ktanino10/copilot-brick-display/docs/licensing.md

# Notices and rights

No blanket license has been selected for this project's original code, CAD, artwork, or documents.
Public availability is not a statement that all uses are permitted. Ask the repository owner
about reuse terms. This file does not relabel third-party components.

Third-party material intentionally redistributed:

| Material | License / notice location | Purpose |
| --- | --- | --- |
| Three.js 0.180.0 | MIT, `site/vendor/THREE-LICENSE.txt` | Local browser 3D runtime |
| B612 Mono Bold | SIL Open Font License 1.1, `resources/fonts/OFL.txt` | Exact approved message outlines |
| Barlow Condensed Bold / Black | SIL Open Font License 1.1, `resources/fonts/barlow-condensed/OFL.txt` | Main-line openings and enlarged URL lettering |

Python packages, FreeCAD, Blender and ffmpeg are build/runtime tools rather than vendored
application binaries. Their respective licenses remain applicable. Package versions are pinned
where installed for this project. Source-reference PDFs and unmodified private/reference photographs
are not copied into the public package.

The [build log](build-log.ja.md) includes only privacy-redacted derivatives of user-supplied progress
photographs, authorized for this project's public and private repository build records.
The photographs remain the rights holder's material: no model/library license automatically
applies to them, and this permission is not CC0, third-party redistribution permission or approval
to repost to MakerWorld or other services. Original photos and identifying metadata are not distributed.

The unmodified Bold font was obtained from the official Google Fonts `ofl/barlowcondensed`
directory at commit `e44c4b011a820c2cbe2fd2cfa8052037d7edb571`.
Its SHA256 is `e476562ec9c1e16cf16475895b511f08c804f438cc9a9f80a44ea50a0eeb5b65`.
The OFL notice is retained unchanged. Per-glyph manufactured counter edits do not modify or relicense the font file.

The new front logo is a supported 3D relief derived from the user's supplied GitHub mark.
Only the derived contours and manufactured geometry are included; the input raster is not distributed.
This does not grant a blanket trademark license or claim official status.

LEGO, Bambu Lab and GitHub names identify references, intended interfaces, tools or the public
profile URL. This is an original, unofficial personal display model. It is not an official LEGO
or GitHub product and has no endorsement or compatibility certification from those organizations.
