ktanino10/copilot-brick-display/site/media/A-base-front.png

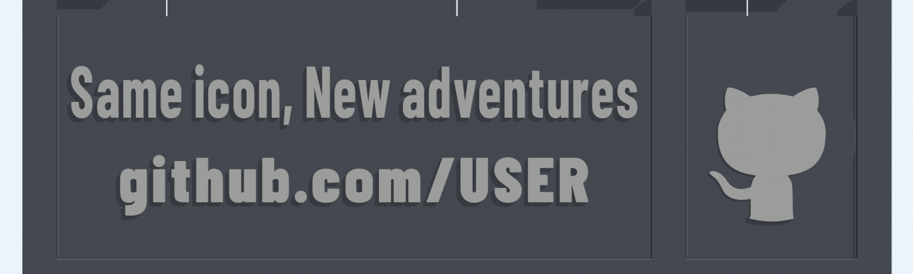
site/media/A-base-front.png
