ktanino10/copilot-brick-display/site/media/A-compare.png

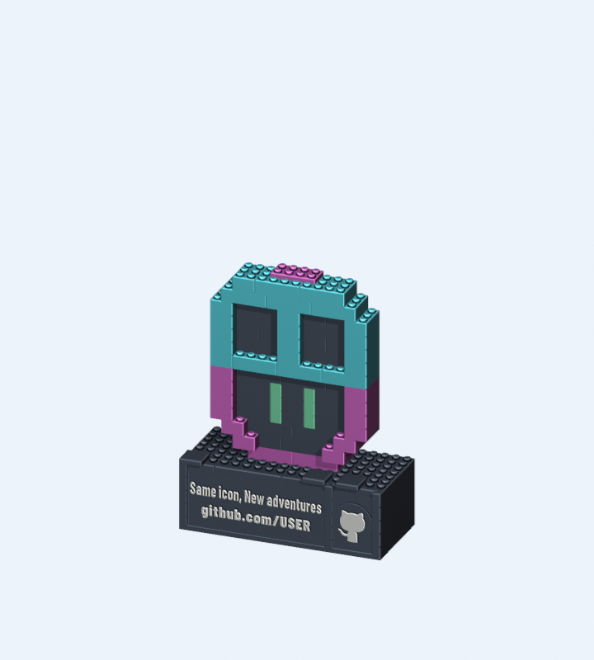
site/media/A-compare.png
