ktanino10/copilot-brick-display/site/media/A-hero.png

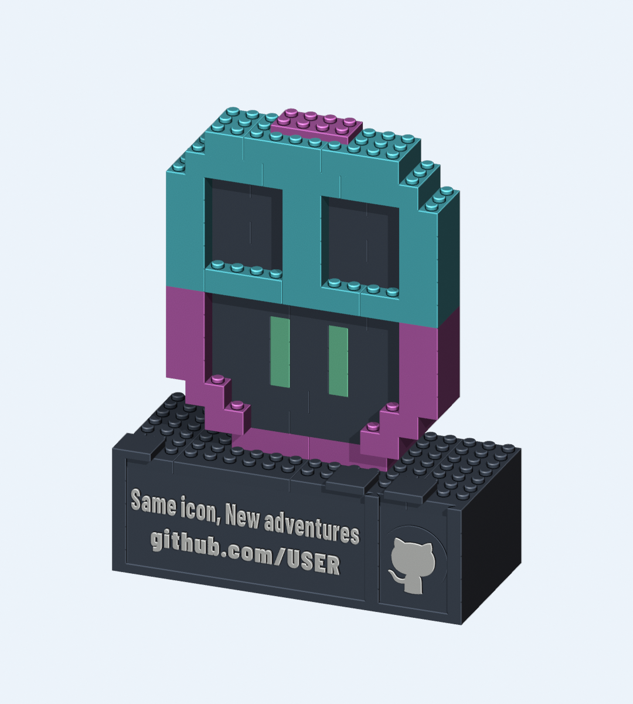
site/media/A-hero.png
