ktanino10/copilot-brick-display/site/media/B-base-front.png

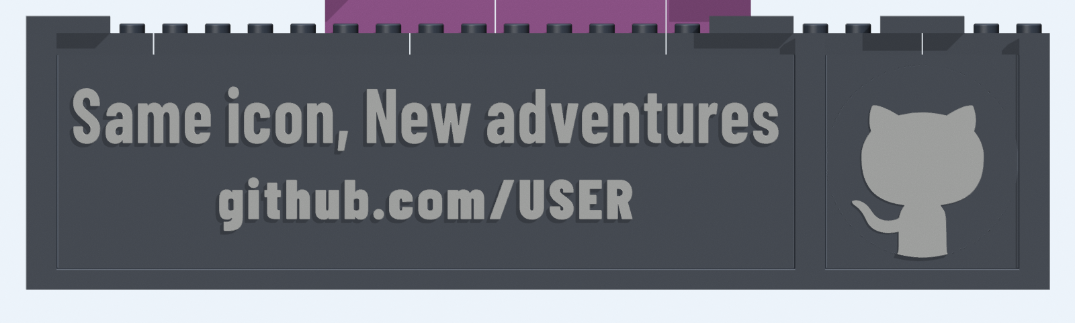
site/media/B-base-front.png
