ktanino10/copilot-brick-display/site/media/B-compare.png

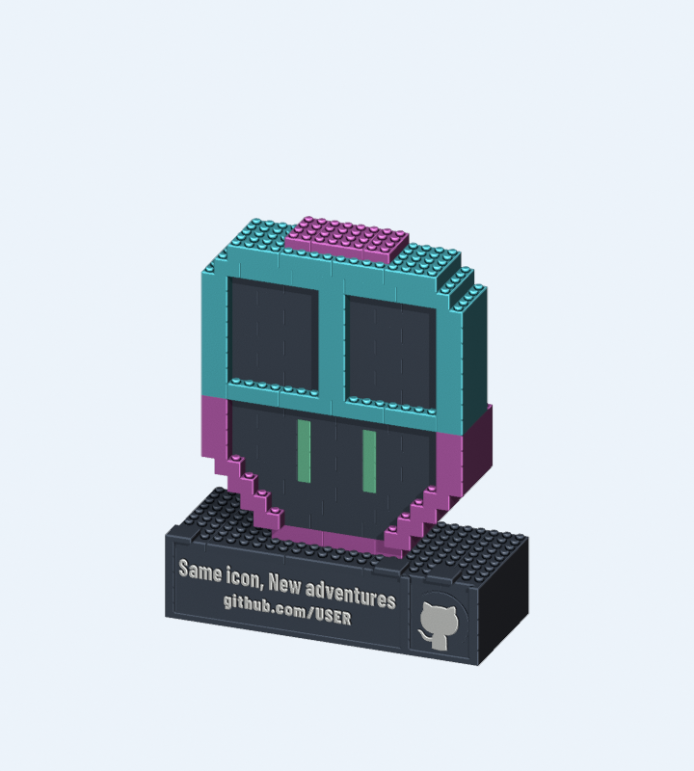
site/media/B-compare.png
