ktanino10/copilot-brick-display/site/media/B-hero.png

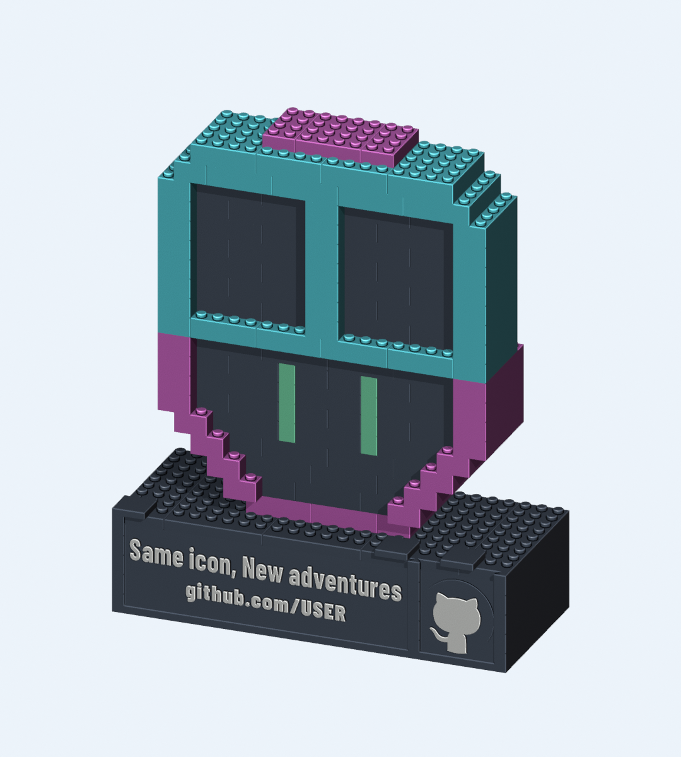
site/media/B-hero.png
