ktanino10/copilot-brick-display/site/media/C-base-front.png

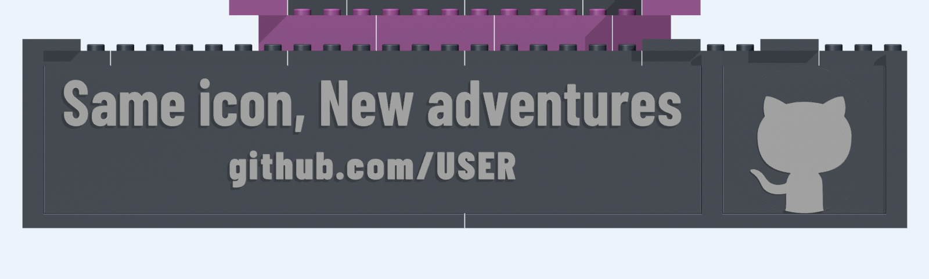
site/media/C-base-front.png
