ktanino10/copilot-brick-display/site/media/C-compare.png

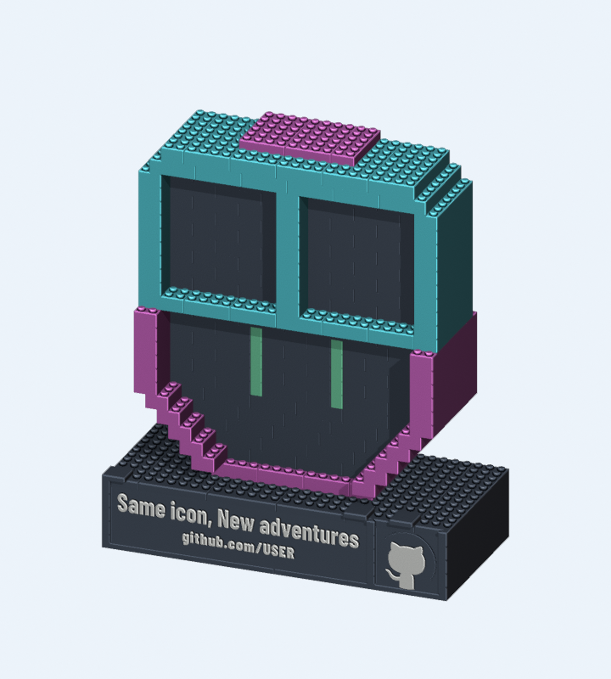
site/media/C-compare.png
