ktanino10/copilot-brick-display/site/media/lettering/A-lettering-before-after.png

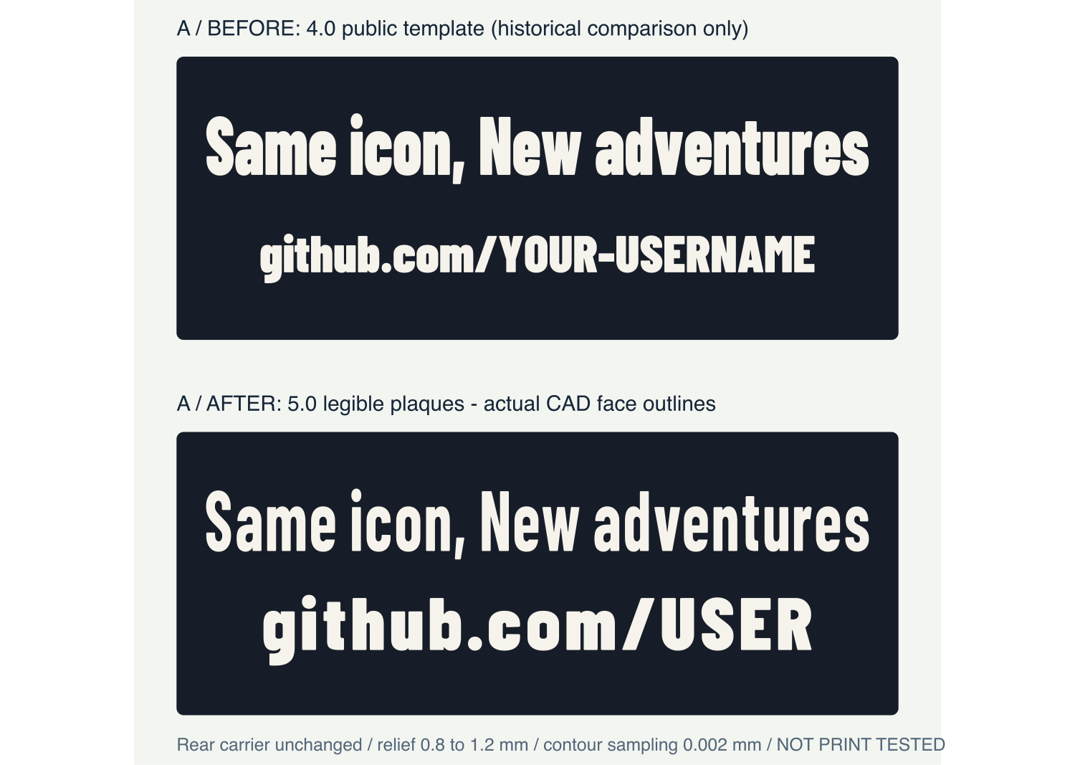
site/media/lettering/A-lettering-before-after.png
