ktanino10/copilot-brick-display/site/media/lettering/C-lettering-before-after.png

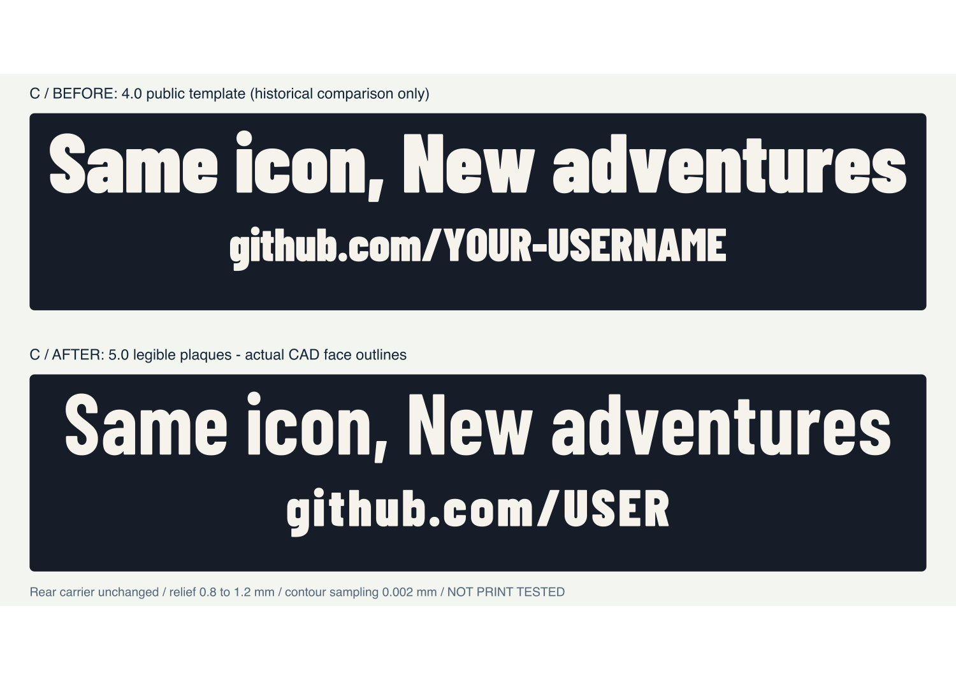
site/media/lettering/C-lettering-before-after.png
