ktanino10/copilot-brick-display/site/assembly-guide/media/B-black-04-base-parts.png

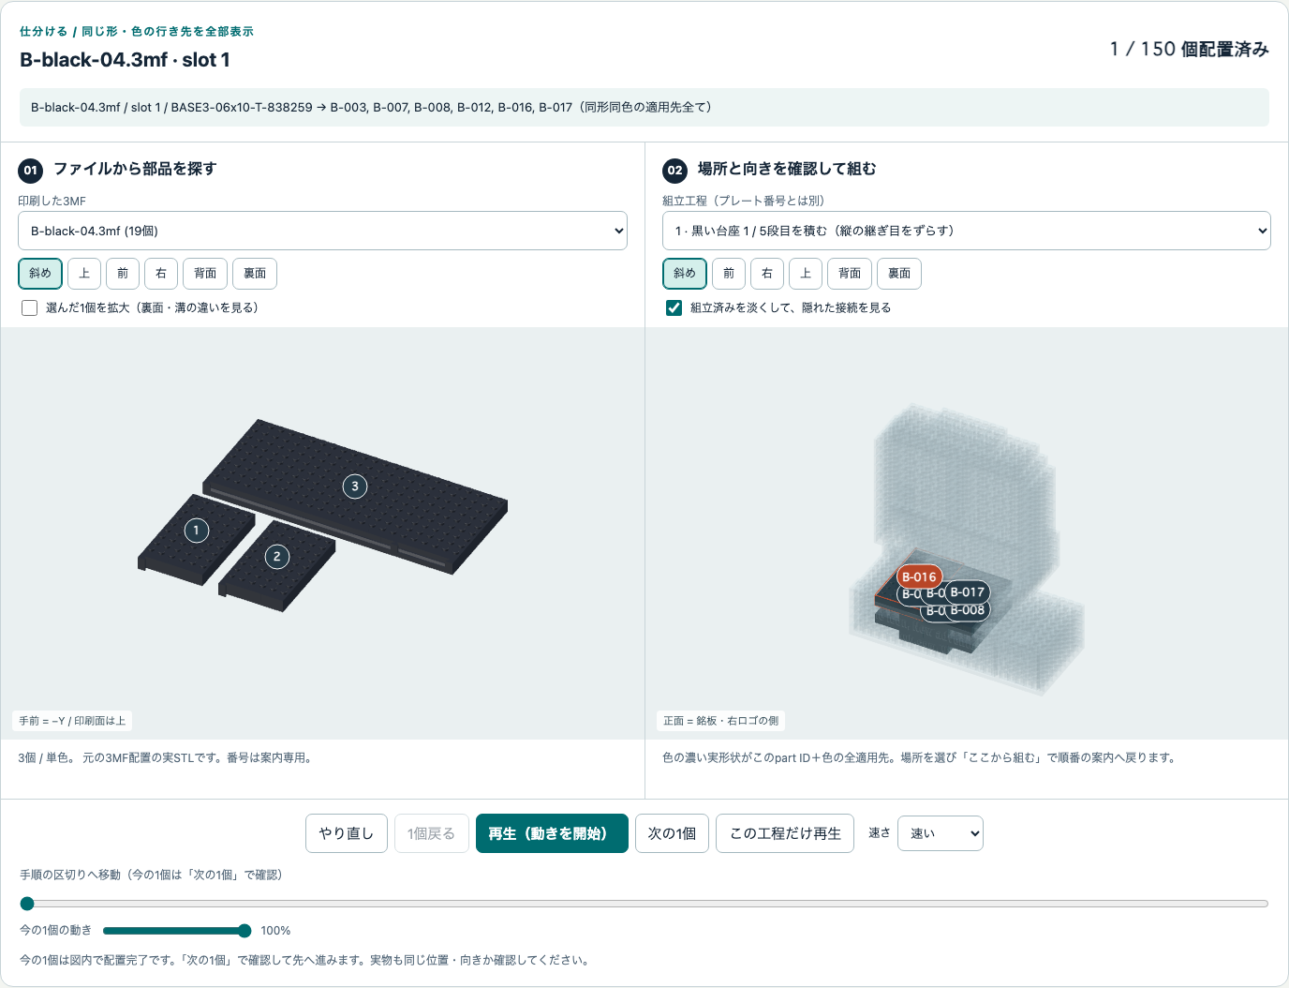
site/assembly-guide/media/B-black-04-base-parts.png
