ktanino10/copilot-brick-display/site/downloads/A/plates/A-green-01.3mf

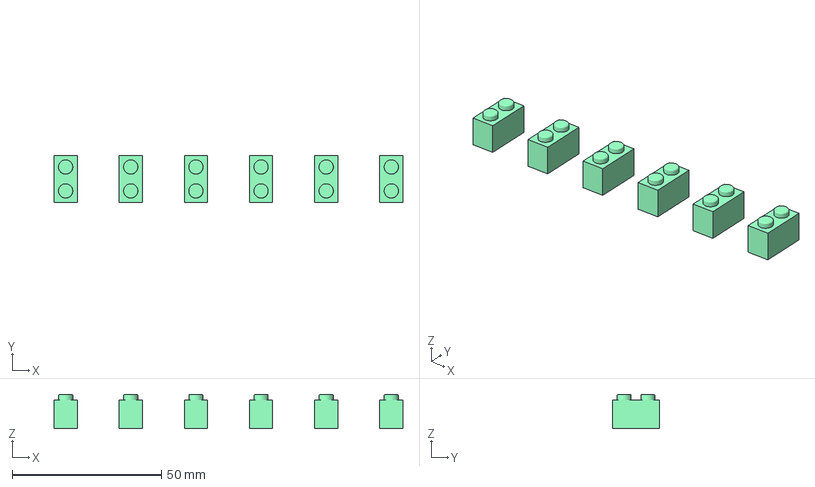
[picture p68: CAD file, 2026-09-19]
site/downloads/A/plates/A-green-01.3mf
116.8 x 15.8 x 11.4 mm
BR-01x02-H096 x 6
