ktanino10/copilot-brick-display/site/downloads/B/plates/B-cyan-02.3mf

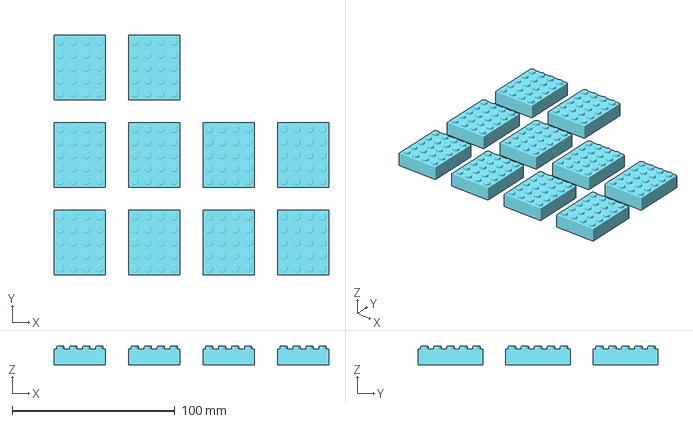
[picture p69: CAD file, 2026-09-19]
site/downloads/B/plates/B-cyan-02.3mf
169.2 x 147.4 x 11.4 mm
BR-04x05-H096 x 10
