ktanino10/copilot-brick-display/site/downloads/C/plates/C-black-16.3mf

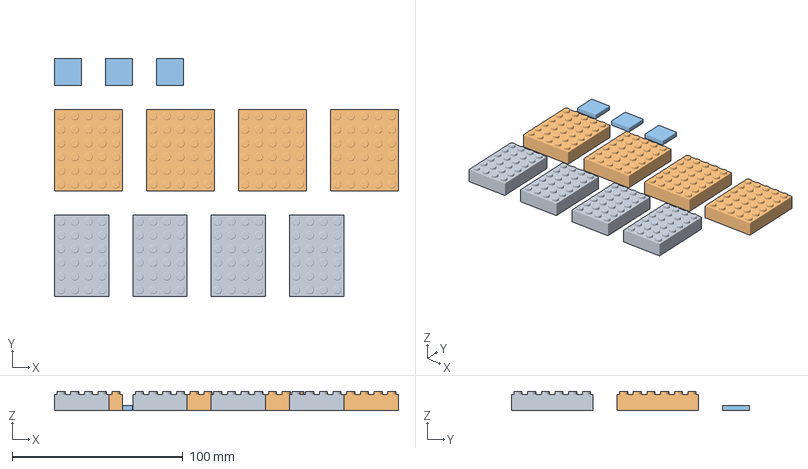
[picture p70: CAD file, 2026-09-19]
site/downloads/C/plates/C-black-16.3mf
201.2 x 139.4 x 11.4 mm
BR-04x06-H096 x 4
BR-05x06-H096 x 4
NP3-KEEPER x 3
