ktanino10/copilot-brick-display/site/downloads/parts/BASE3-06x08-T-b8aa05.stl

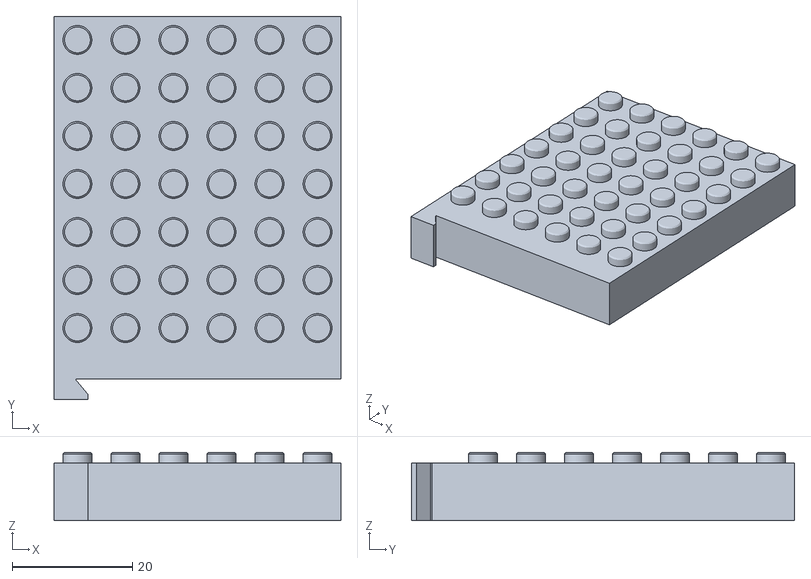
[picture p71: CAD file, 2026-09-19]
site/downloads/parts/BASE3-06x08-T-b8aa05.stl
47.8 x 63.8 x 11.4
