ktanino10/copilot-brick-display/site/downloads/A/plates/A-black-04.3mf

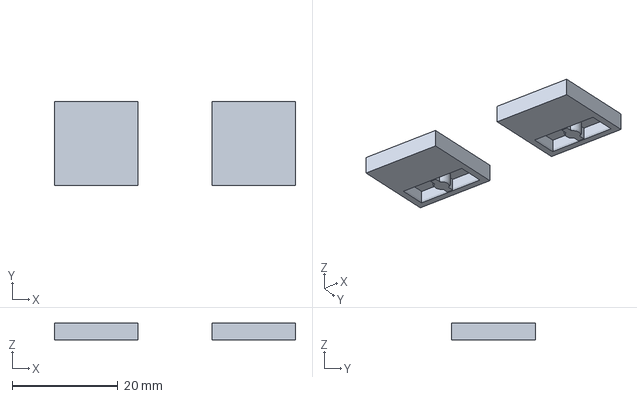
[picture p72: CAD file, 2026-09-19]
site/downloads/A/plates/A-black-04.3mf
45.6 x 15.8 x 3.20 mm
NP3-KEEPER x 2
