ktanino10/copilot-brick-display/site/downloads/B/plates/B-magenta-02.3mf

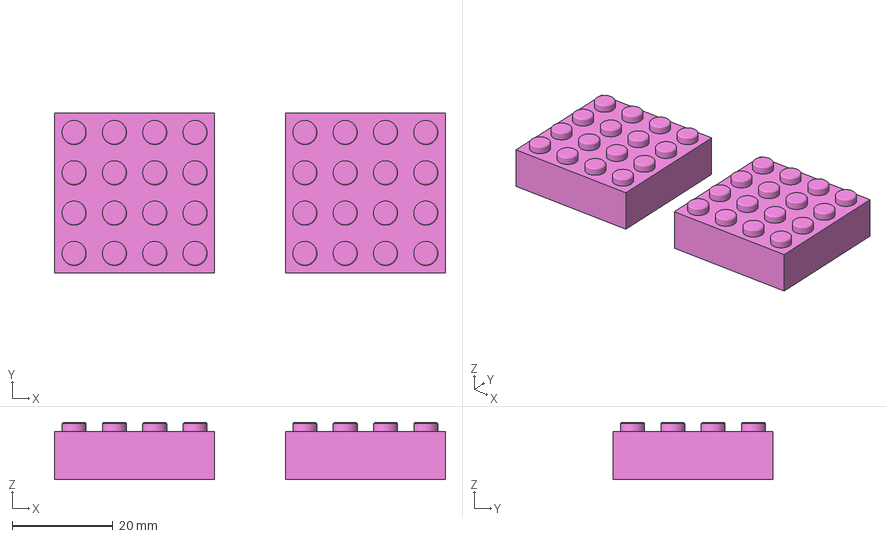
[picture p73: CAD file, 2026-09-19]
site/downloads/B/plates/B-magenta-02.3mf
77.6 x 31.8 x 11.4 mm
BR-04x04-H096 x 2
