ktanino10/copilot-brick-display/site/downloads/parts/BASE3-06x14-T-f6d8b7.stl

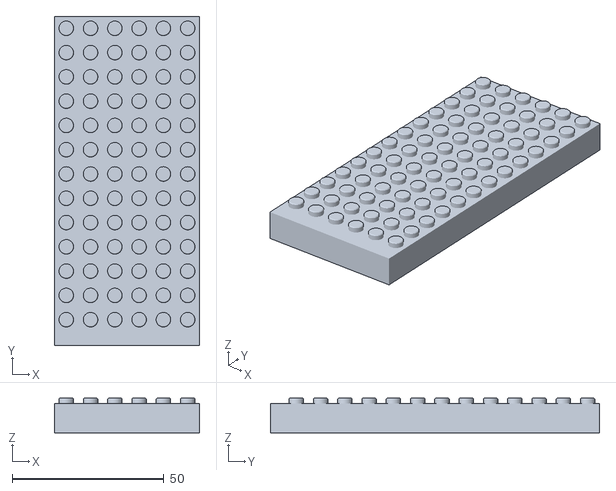
[picture p74: CAD file, 2026-09-19]
site/downloads/parts/BASE3-06x14-T-f6d8b7.stl
47.8 x 108.4 x 11.4
