ktanino10/copilot-brick-display/site/downloads/A/plates/A-black-02.3mf

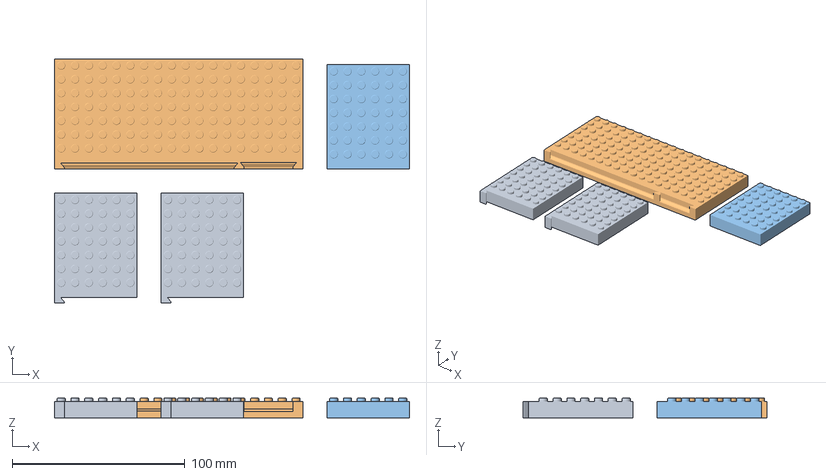
[picture p75: CAD file, 2026-09-19]
site/downloads/A/plates/A-black-02.3mf
205.6 x 141.6 x 11.4 mm
BASE3-06x08-T-b8aa05 x 2
BASE3-18x08-B-a4853c
BASE3-06x08-T-9cb610
