ktanino10/copilot-brick-display/site/downloads/B/plates/B-black-02.3mf

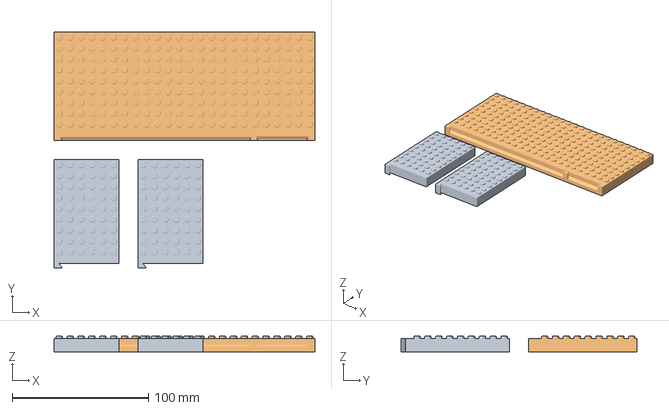
[picture p76: CAD file, 2026-09-19]
site/downloads/B/plates/B-black-02.3mf
191.8 x 173.6 x 11.4 mm
BASE3-06x10-T-e1945a x 2
BASE3-24x10-B-562406
