ktanino10/copilot-brick-display/site/downloads/C/plates/C-black-03.3mf

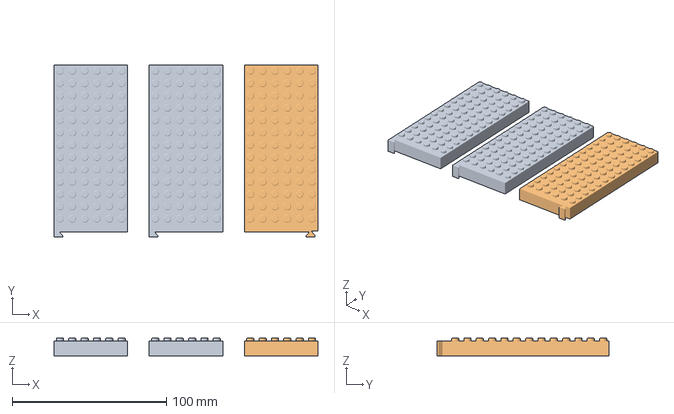
[picture p77: CAD file, 2026-09-19]
site/downloads/C/plates/C-black-03.3mf
171.4 x 111.8 x 11.4 mm
BASE3-06x14-T-72d551 x 2
BASE3-06x14-T-afd244
