ktanino10/copilot-brick-display/site/downloads/parts/BASE3-03x14-T-08700f.stl

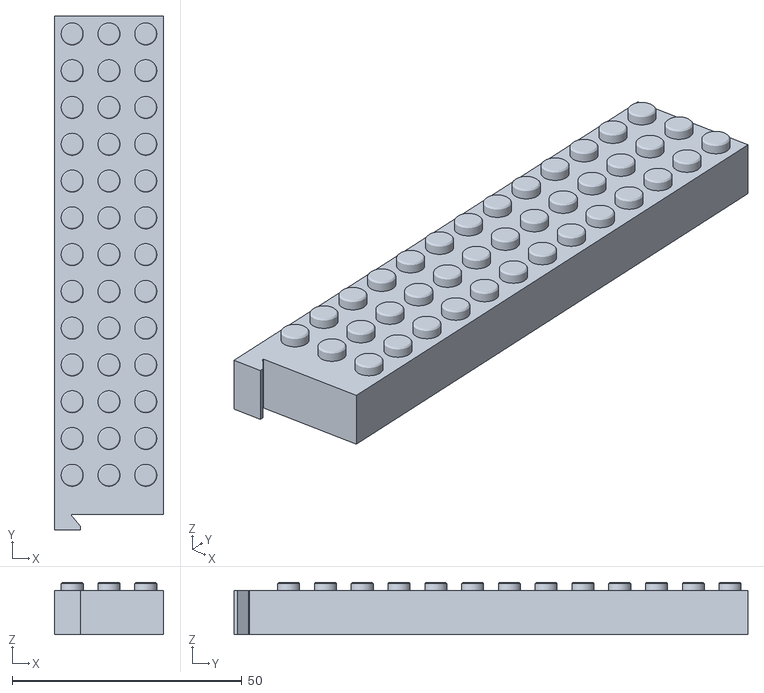
[picture p78: CAD file, 2026-09-19]
site/downloads/parts/BASE3-03x14-T-08700f.stl
23.8 x 111.8 x 11.4
