ktanino10/copilot-brick-display/site/downloads/A/plates/A-magenta-01.3mf

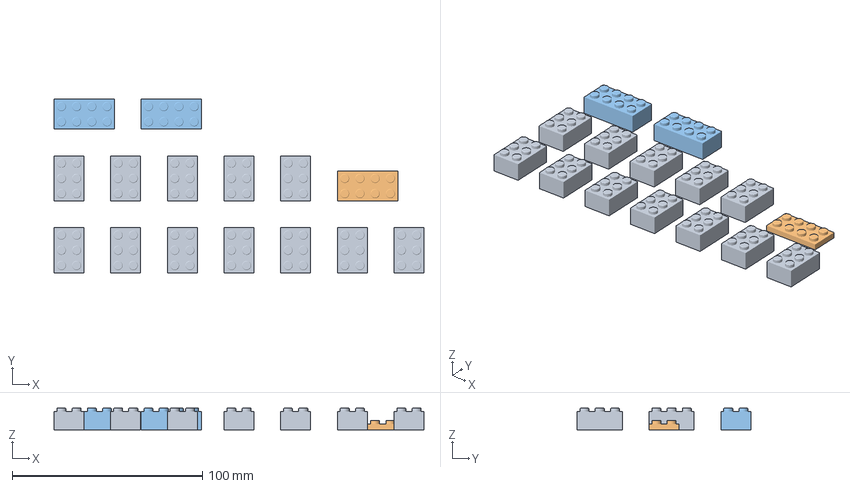
[picture p79: CAD file, 2026-09-19]
site/downloads/A/plates/A-magenta-01.3mf
194.6 x 91.4 x 11.4 mm
BR-02x03-H096 x 12
BR-04x02-H032
BR-04x02-H096 x 2
