ktanino10/copilot-brick-display/site/downloads/B/plates/B-black-05.3mf

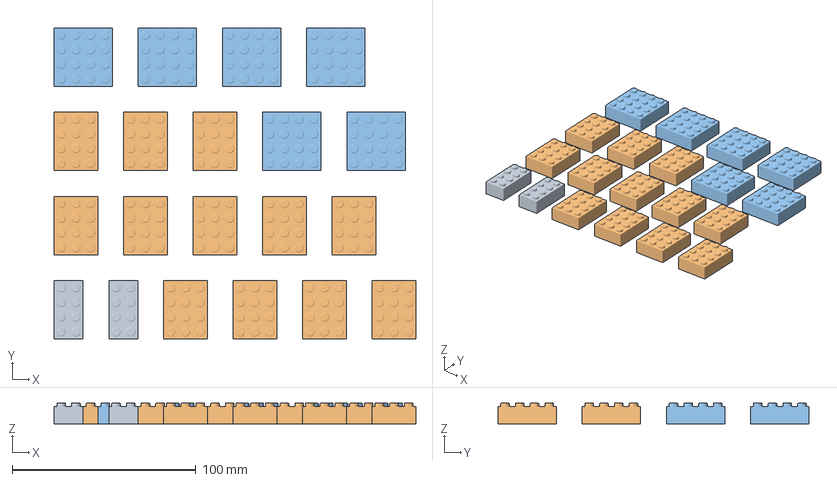
[picture p80: CAD file, 2026-09-19]
site/downloads/B/plates/B-black-05.3mf
196.8 x 169.2 x 11.4 mm
BR-02x04-H096 x 2
BR-03x04-H096 x 12
BR-04x04-H096 x 6
