ktanino10/copilot-brick-display/site/downloads/C/plates/C-green-01.3mf

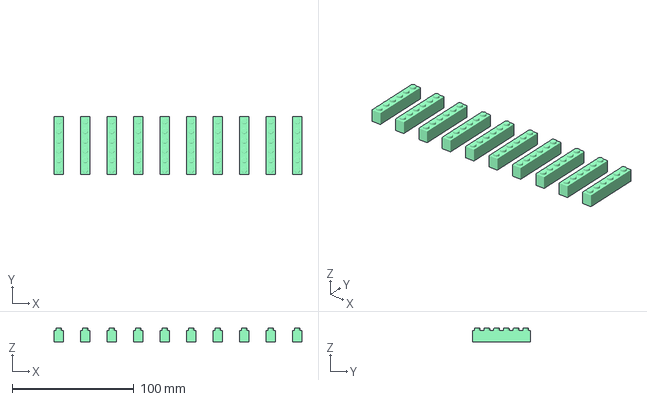
[picture p81: CAD file, 2026-09-19]
site/downloads/C/plates/C-green-01.3mf
204.0 x 47.8 x 11.4 mm
BR-01x06-H096 x 10
