ktanino10/copilot-brick-display/site/downloads/B/plates/B-black-06.3mf

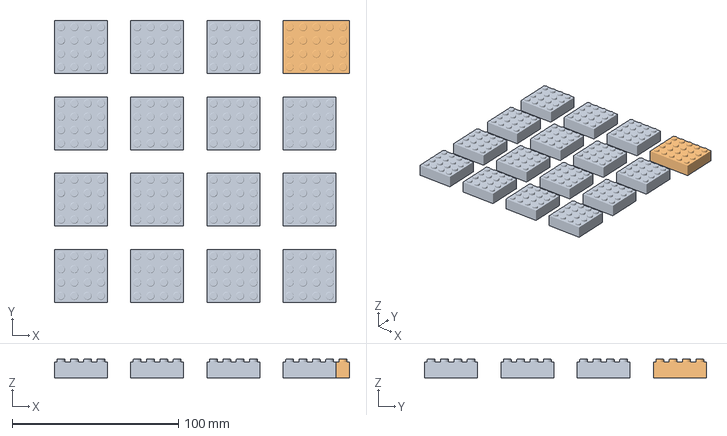
[picture p82: CAD file, 2026-09-19]
site/downloads/B/plates/B-black-06.3mf
177.2 x 169.2 x 11.4 mm
BR-04x04-H096 x 15
BR-05x04-H096
