ktanino10/copilot-brick-display/site/downloads/C/plates/C-magenta-03.3mf

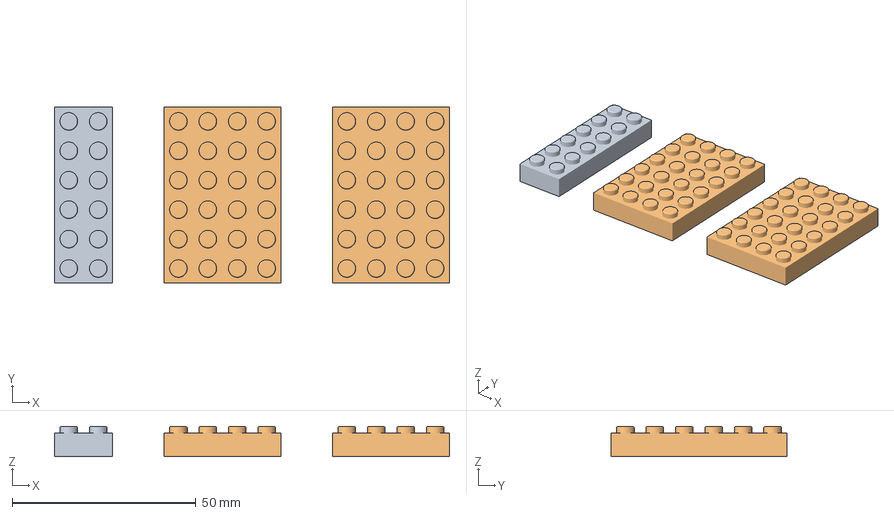
[picture p83: CAD file, 2026-09-19]
site/downloads/C/plates/C-magenta-03.3mf
107.4 x 47.8 x 8.20 mm
BR-02x06-H064
BR-04x06-H064 x 2
