ktanino10/copilot-brick-display/site/downloads/parts/BASE3-06x10-T-e1945a.stl

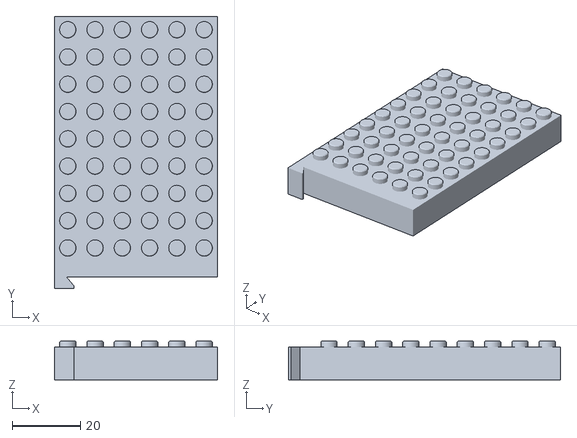
[picture p84: CAD file, 2026-09-19]
site/downloads/parts/BASE3-06x10-T-e1945a.stl
47.8 x 79.8 x 11.4
