ktanino10/copilot-brick-display/site/downloads/A/plates/A-black-to-white-z2p8-01.3mf

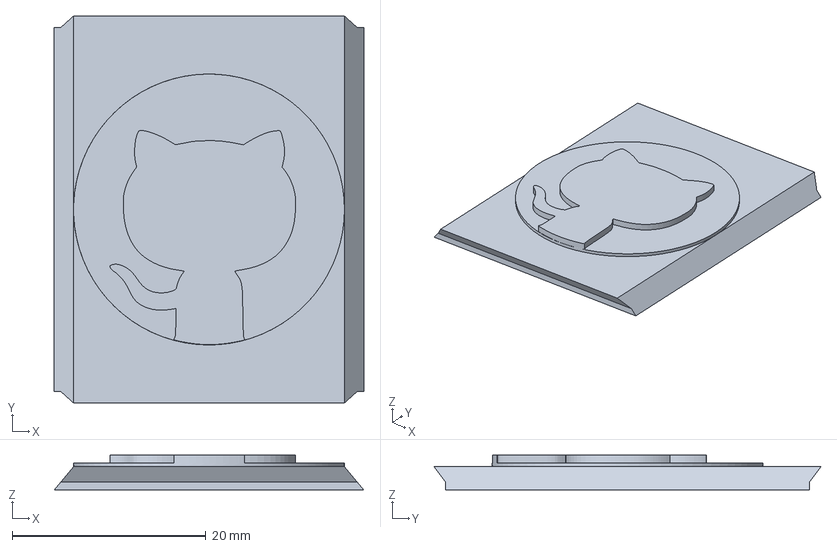
[picture p85: CAD file, 2026-09-19]
site/downloads/A/plates/A-black-to-white-z2p8-01.3mf
32.0 x 40.0 x 3.60 mm
