ktanino10/copilot-brick-display/site/downloads/B/plates/B-magenta-01.3mf

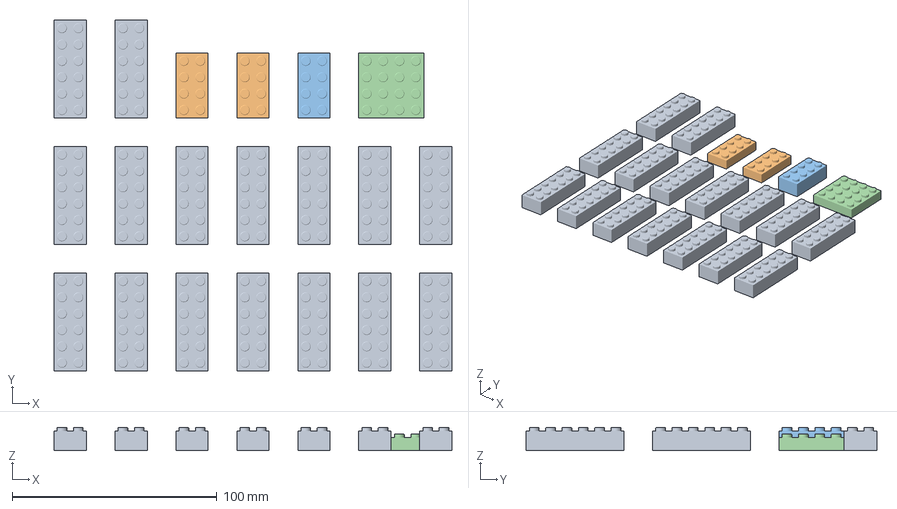
[picture p86: CAD file, 2026-09-19]
site/downloads/B/plates/B-magenta-01.3mf
194.6 x 171.4 x 11.4 mm
BR-02x06-H096 x 16
BR-02x04-H064 x 2
BR-02x04-H096
BR-04x04-H064
