ktanino10/copilot-brick-display/site/downloads/C/plates/C-black-to-white-z2p8-01.3mf

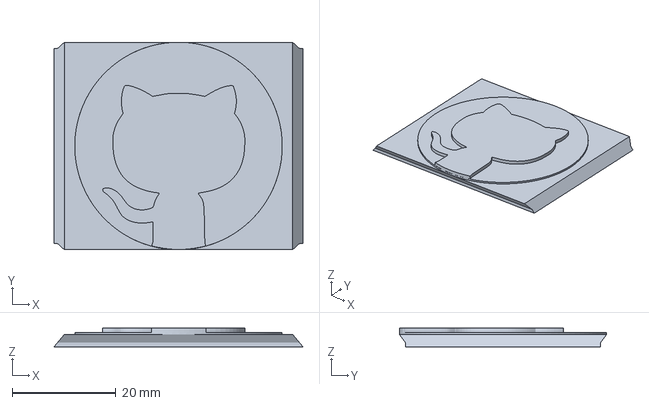
[picture p87: CAD file, 2026-09-19]
site/downloads/C/plates/C-black-to-white-z2p8-01.3mf
48.0 x 40.0 x 3.60 mm
