ktanino10/copilot-brick-display/site/downloads/parts/NP3-FIT-SOCKET-C15.stl

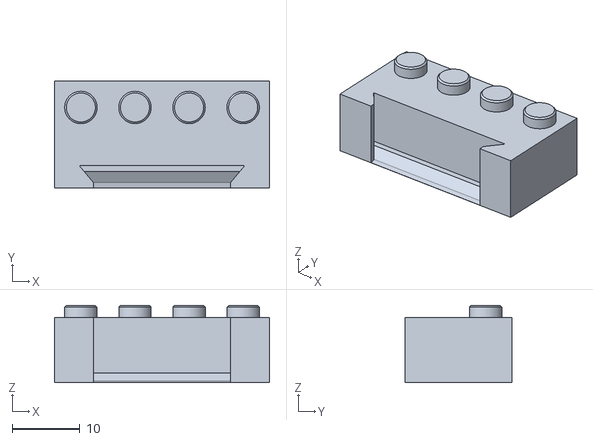
[picture p88: CAD file, 2026-09-19]
site/downloads/parts/NP3-FIT-SOCKET-C15.stl
31.8 x 15.8 x 11.4
