ktanino10/copilot-brick-display/site/downloads/C/plates/C-black-10.3mf

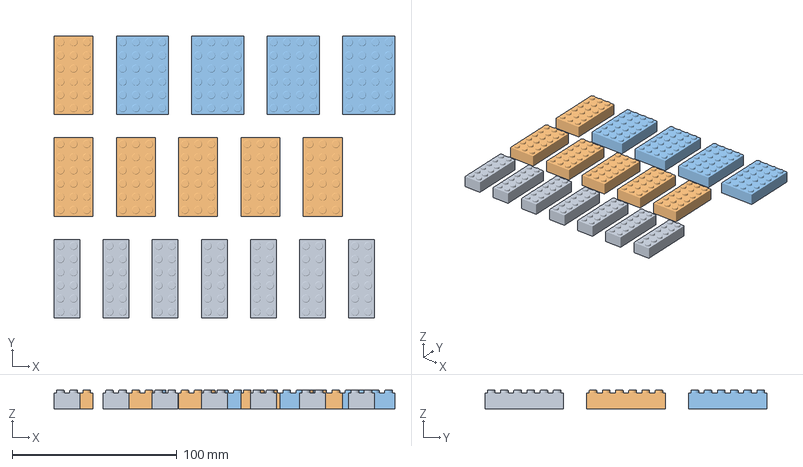
[picture p90: CAD file, 2026-09-19]
site/downloads/C/plates/C-black-10.3mf
207.0 x 171.4 x 11.4 mm
BR-02x06-H096 x 7
BR-03x06-H096 x 6
BR-04x06-H096 x 4
