ktanino10/copilot-brick-display/site/downloads/parts/BASE3-15x14-B-2f9fc1.stl

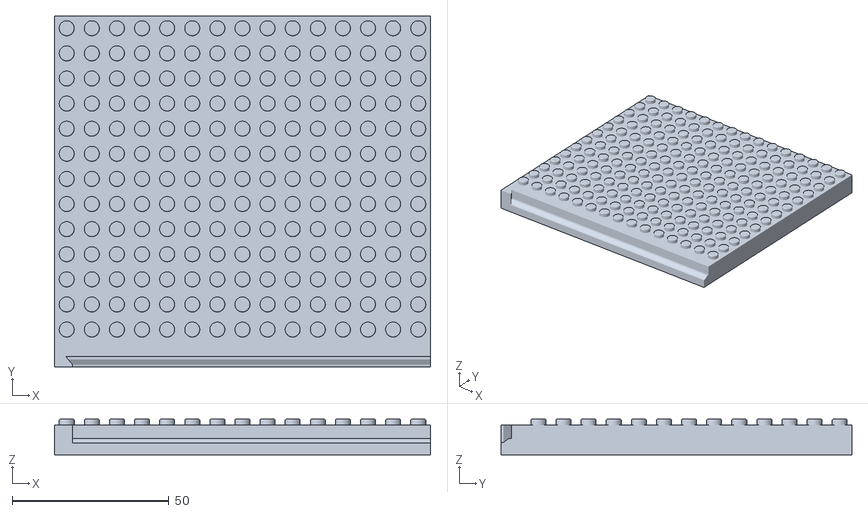
[picture p91: CAD file, 2026-09-19]
site/downloads/parts/BASE3-15x14-B-2f9fc1.stl
119.8 x 111.8 x 11.4
