ktanino10/copilot-brick-display/site/downloads/B/plates/B-black-to-white-z2p8-01.3mf

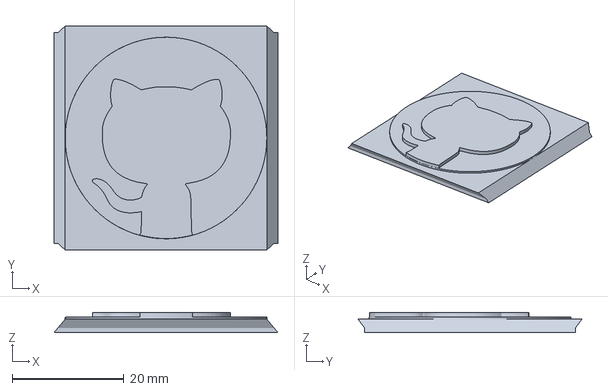
[picture p92: CAD file, 2026-09-19]
site/downloads/B/plates/B-black-to-white-z2p8-01.3mf
40.0 x 40.0 x 3.60 mm
