ktanino10/copilot-brick-display/site/downloads/C/plates/C-magenta-02.3mf

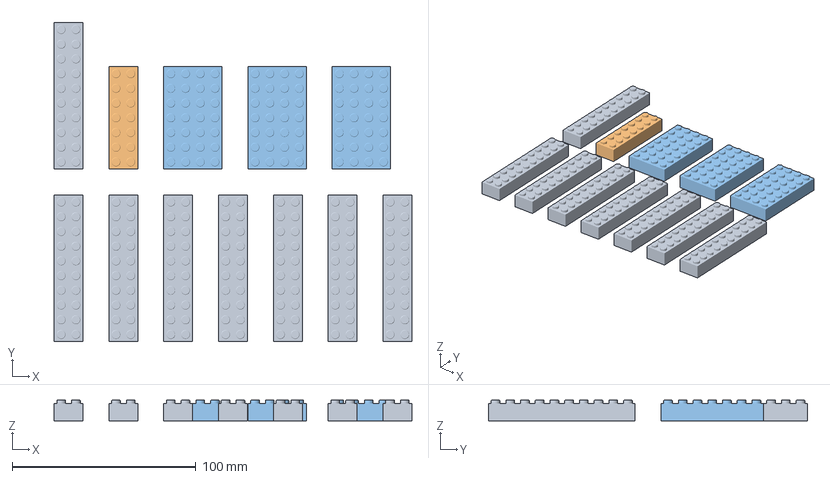
[picture p93: CAD file, 2026-09-19]
site/downloads/C/plates/C-magenta-02.3mf
194.6 x 173.6 x 11.4 mm
BR-02x10-H096 x 8
BR-02x07-H096
BR-04x07-H096 x 3
