ktanino10/copilot-brick-display/site/downloads/parts/BASE3-18x08-B-a4853c.stl

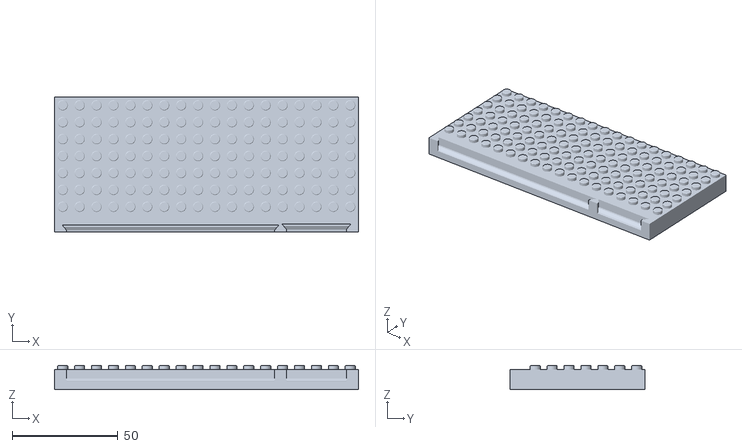
[picture p94: CAD file, 2026-09-19]
site/downloads/parts/BASE3-18x08-B-a4853c.stl
143.8 x 63.8 x 11.4
