ktanino10/copilot-brick-display/site/downloads/C/plates/C-magenta-01.3mf

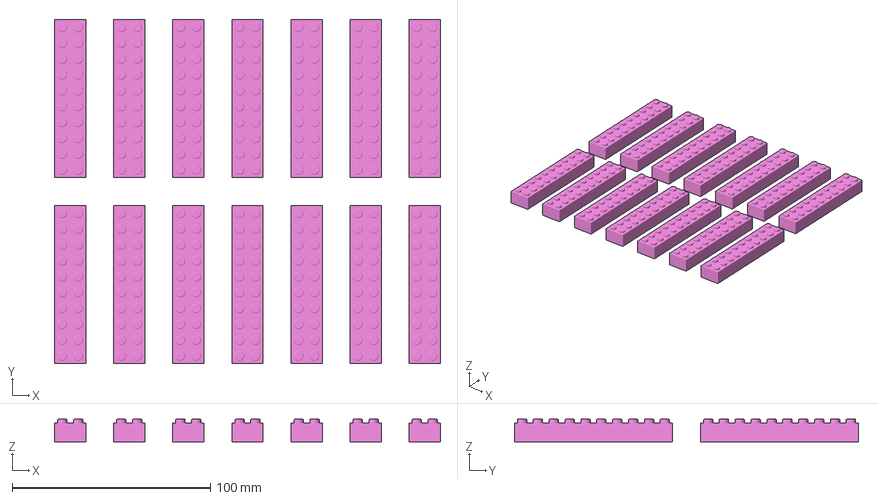
[picture p96: CAD file, 2026-09-19]
site/downloads/C/plates/C-magenta-01.3mf
194.6 x 173.6 x 11.4 mm
BR-02x10-H096 x 14
