ktanino10/copilot-brick-display/site/downloads/parts/BASE3-24x10-B-562406.stl

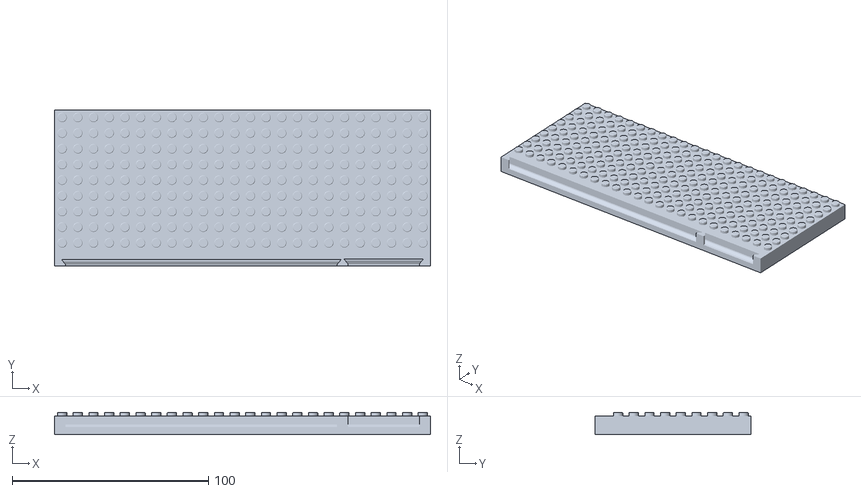
[picture p97: CAD file, 2026-09-19]
site/downloads/parts/BASE3-24x10-B-562406.stl
191.8 x 79.8 x 11.4
