ktanino10/copilot-brick-display/site/downloads/B/plates/B-black-03.3mf

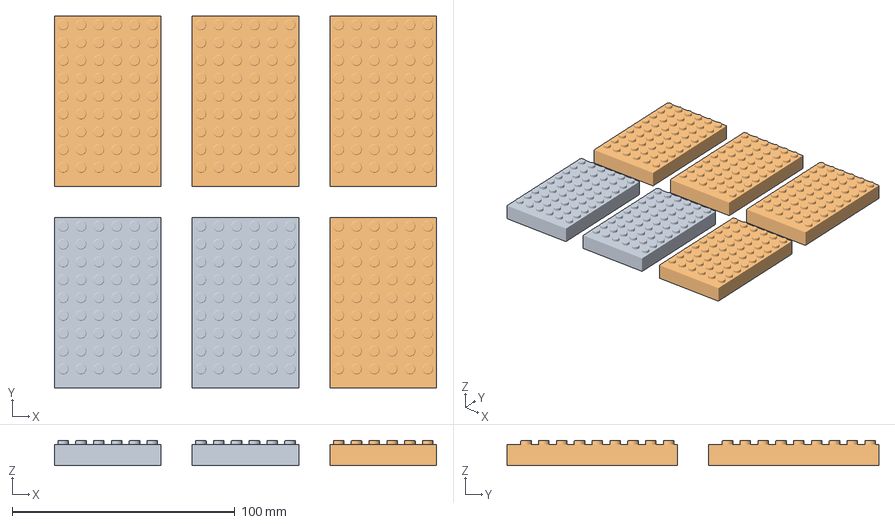
[picture p98: CAD file, 2026-09-19]
site/downloads/B/plates/B-black-03.3mf
171.4 x 166.8 x 11.4 mm
BASE3-06x10-T-3f87ac x 2
BASE3-06x10-T-838259 x 4
