ktanino10/copilot-brick-display/site/downloads/C/plates/C-cyan-04.3mf

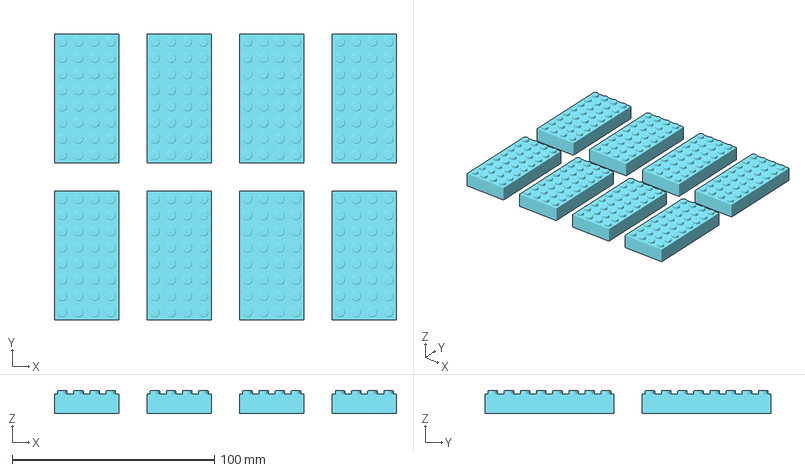
[picture p99: CAD file, 2026-09-19]
site/downloads/C/plates/C-cyan-04.3mf
169.2 x 141.6 x 11.4 mm
BR-04x08-H096 x 8
