ktanino10/copilot-brick-display/site/downloads/C/plates/C-black-04.3mf

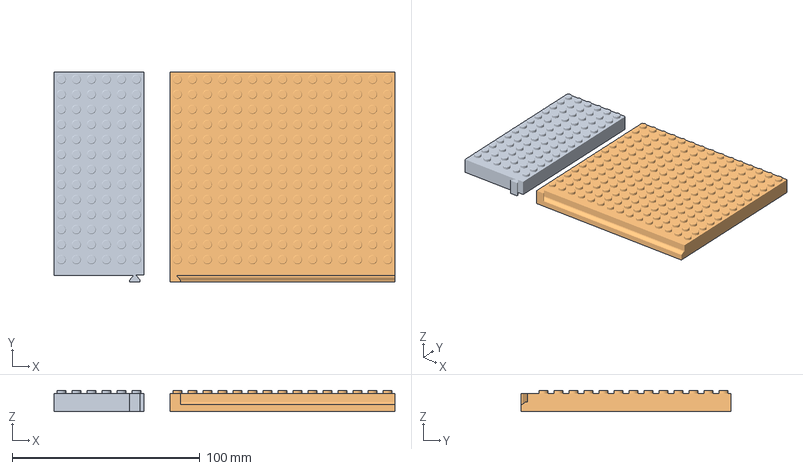
[picture p101: CAD file, 2026-09-19]
site/downloads/C/plates/C-black-04.3mf
181.6 x 111.8 x 11.4 mm
BASE3-06x14-T-afd244
BASE3-15x14-B-2f9fc1
