ktanino10/copilot-brick-display/site/downloads/parts/NP3-FIT-PLAQUE.stl

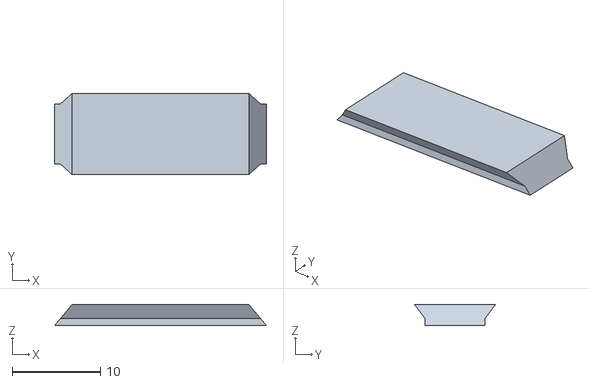
[picture p102: CAD file, 2026-09-19]
site/downloads/parts/NP3-FIT-PLAQUE.stl
24.0 x 9.20 x 2.40
