ktanino10/copilot-brick-display/site/downloads/parts/NP3-KEEPER.stl

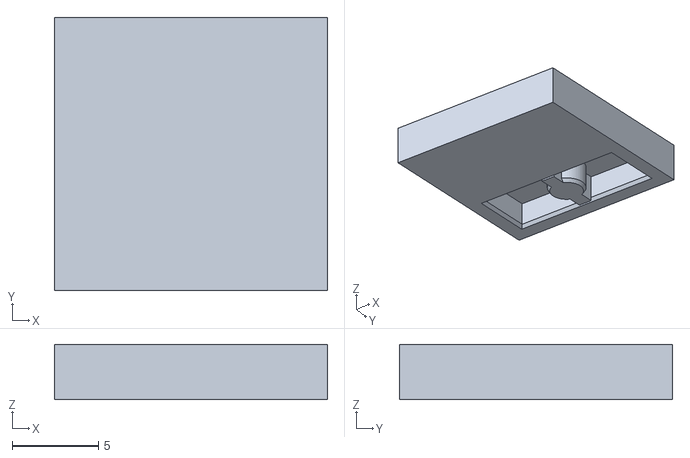
[picture p103: CAD file, 2026-09-19]
site/downloads/parts/NP3-KEEPER.stl
15.8 x 15.8 x 3.20
