ktanino10/copilot-brick-display/site/downloads/parts/BASE3-06x10-T-838259.stl

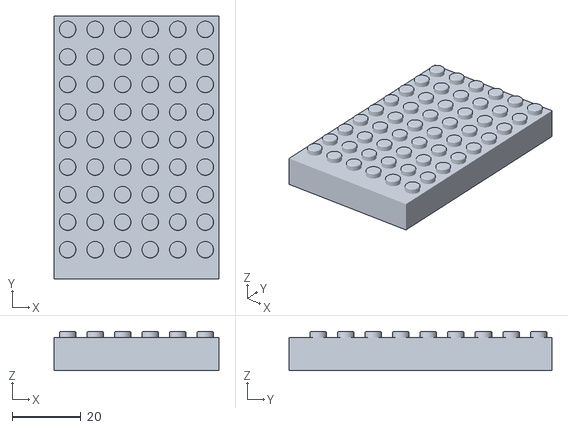
[picture p104: CAD file, 2026-09-19]
site/downloads/parts/BASE3-06x10-T-838259.stl
47.8 x 76.4 x 11.4
