ktanino10/copilot-brick-display/site/downloads/C/plates/C-cyan-05.3mf

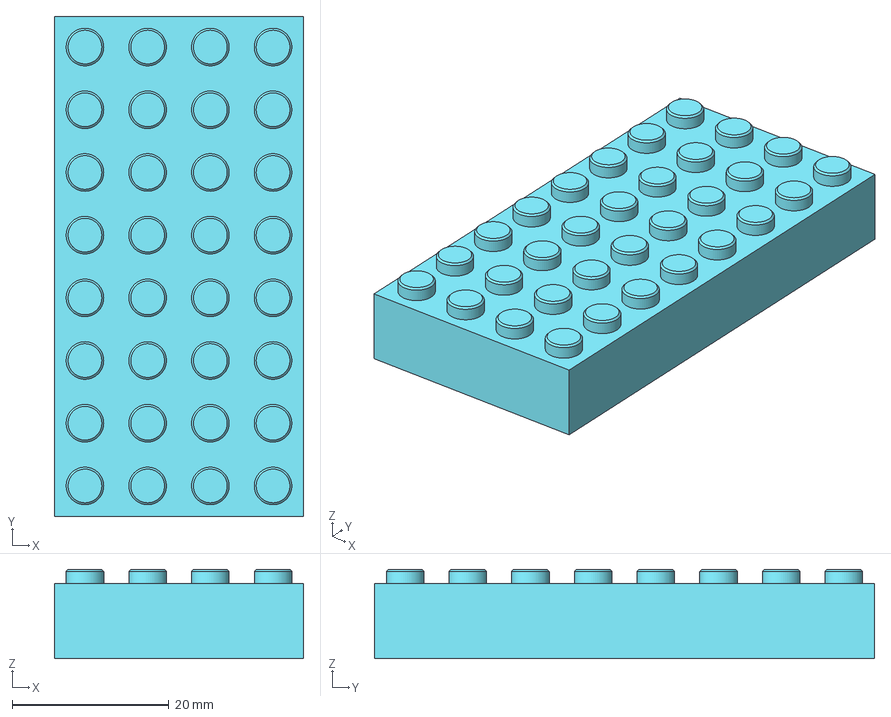
[picture p105: CAD file, 2026-09-19]
site/downloads/C/plates/C-cyan-05.3mf
31.8 x 63.8 x 11.4 mm
