ktanino10/copilot-brick-display/site/downloads/parts/BASE3-03x10-T-aa77a9.stl

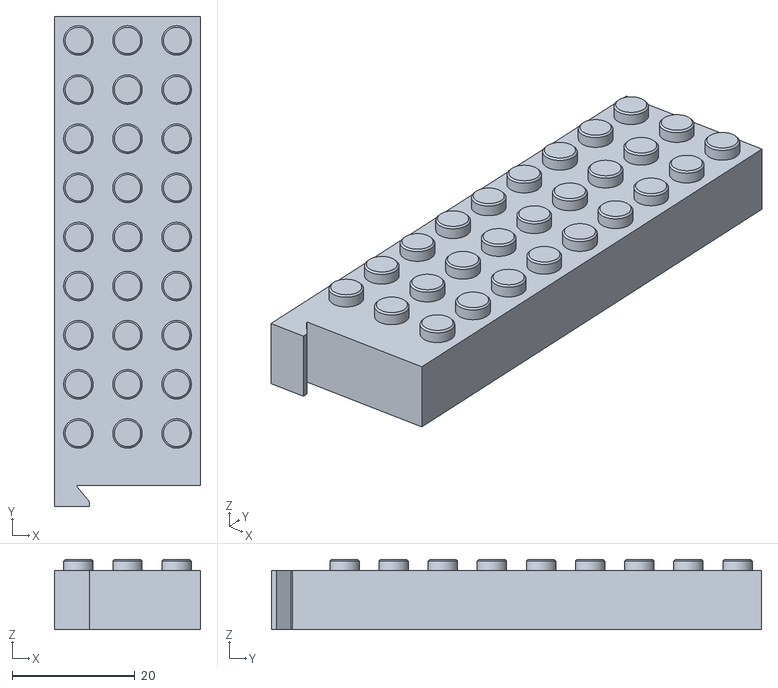
[picture p106: CAD file, 2026-09-19]
site/downloads/parts/BASE3-03x10-T-aa77a9.stl
23.8 x 79.8 x 11.4
