ktanino10/copilot-brick-display/site/downloads/C/plates/C-cyan-01.3mf

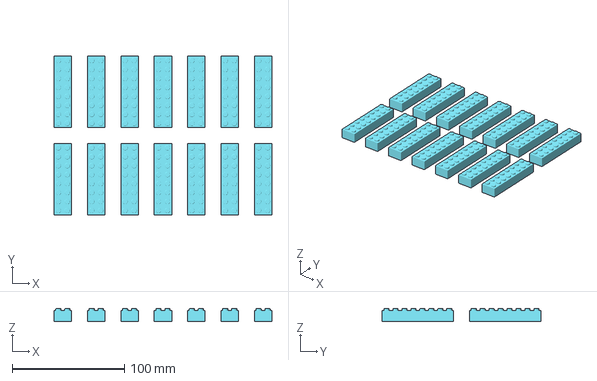
[picture p107: CAD file, 2026-09-19]
site/downloads/C/plates/C-cyan-01.3mf
194.6 x 141.6 x 11.4 mm
BR-02x08-H096 x 14
