ktanino10/copilot-brick-display/site/downloads/parts/BASE3-06x08-T-9cb610.stl

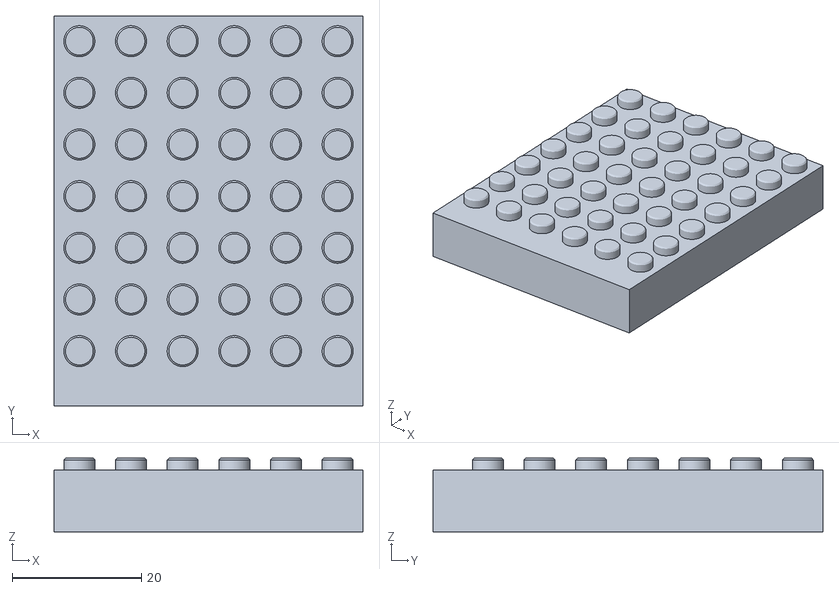
[picture p108: CAD file, 2026-09-19]
site/downloads/parts/BASE3-06x08-T-9cb610.stl
47.8 x 60.4 x 11.4
