ktanino10/copilot-brick-display/site/downloads/C/plates/C-black-01.3mf

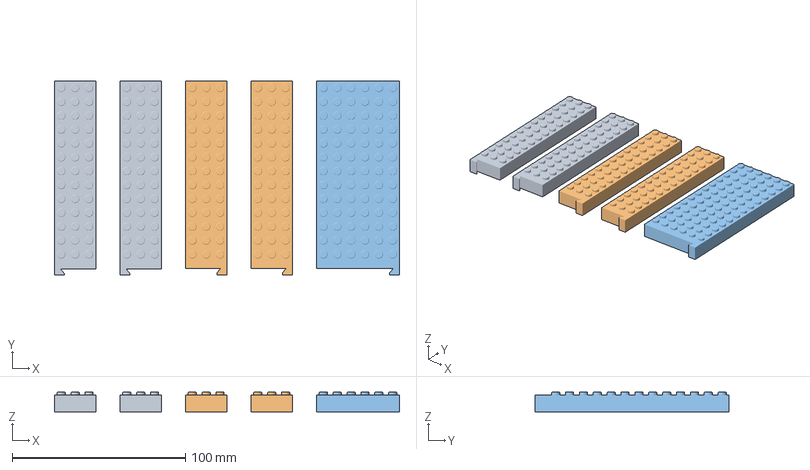
[picture p109: CAD file, 2026-09-19]
site/downloads/C/plates/C-black-01.3mf
199.0 x 111.8 x 11.4 mm
BASE3-03x14-T-08700f x 2
BASE3-03x14-T-d96cba x 2
BASE3-06x14-T-26e6b0
