ktanino10/copilot-brick-display/site/downloads/parts/BASE3-03x08-T-80e081.stl

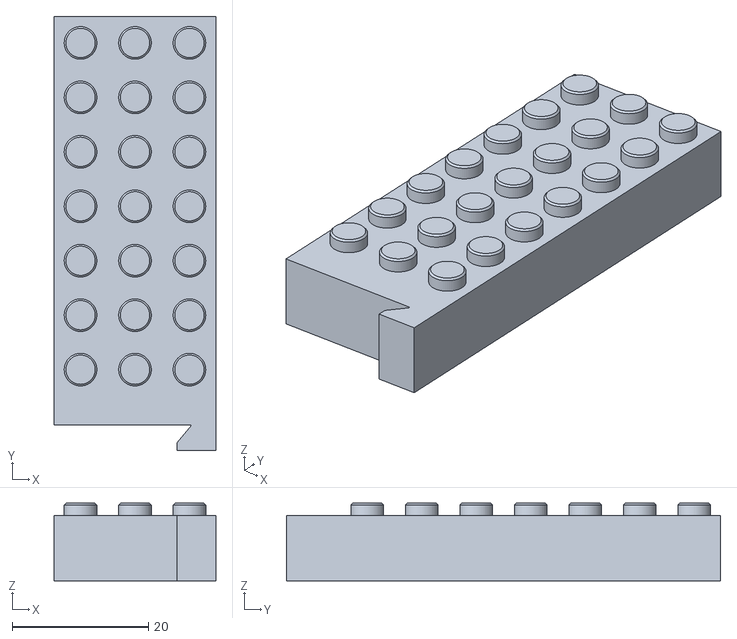
[picture p110: CAD file, 2026-09-19]
site/downloads/parts/BASE3-03x08-T-80e081.stl
23.8 x 63.8 x 11.4
