ktanino10/copilot-brick-display/site/downloads/parts/BR-04x06-H064.stl

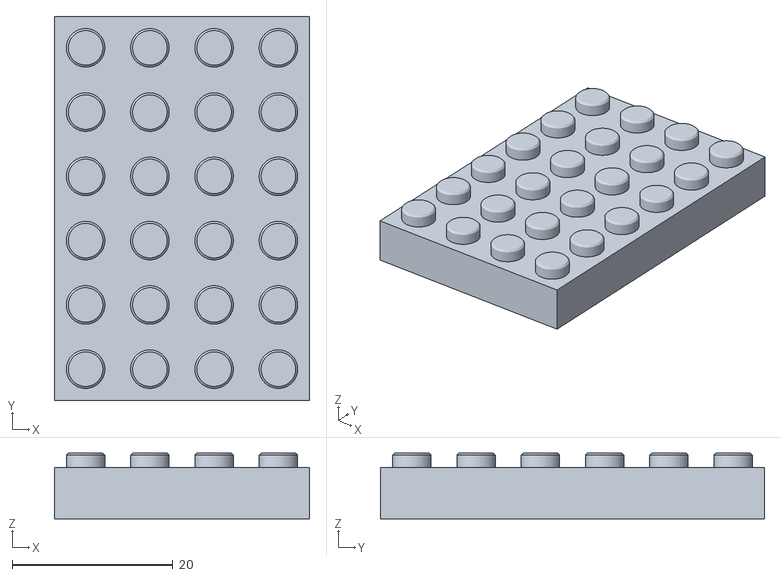
[picture p111: CAD file, 2026-09-19]
site/downloads/parts/BR-04x06-H064.stl
31.8 x 47.8 x 8.20
