ktanino10/copilot-brick-display/site/downloads/parts/BR-02x04-H064.stl

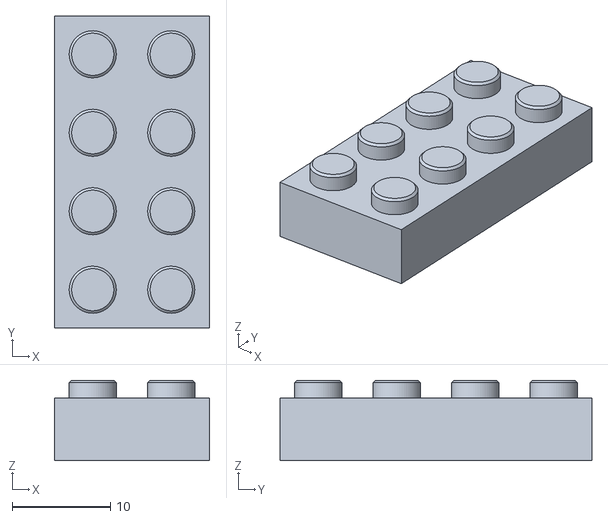
[picture p112: CAD file, 2026-09-19]
site/downloads/parts/BR-02x04-H064.stl
15.8 x 31.8 x 8.20
