ktanino10/copilot-brick-display/site/downloads/parts/BR-03x04-H096.stl

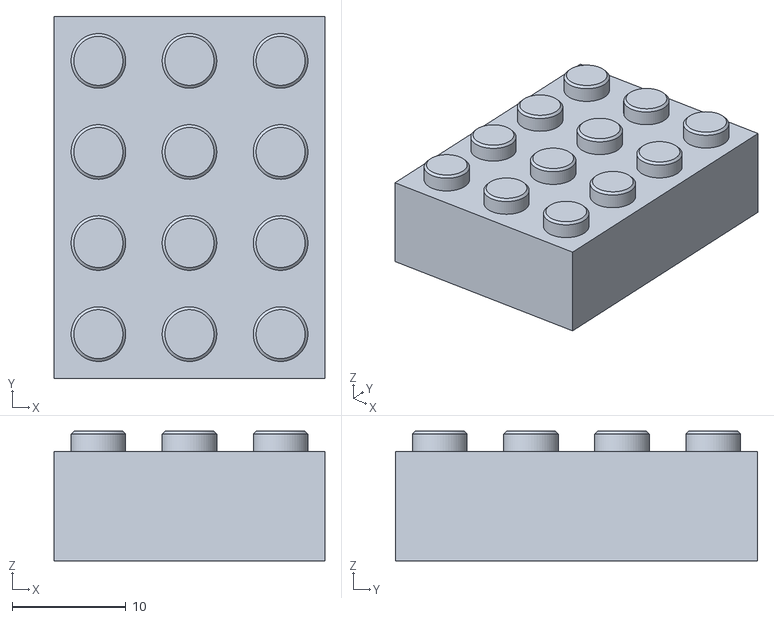
[picture p113: CAD file, 2026-09-19]
site/downloads/parts/BR-03x04-H096.stl
23.8 x 31.8 x 11.4
