ktanino10/copilot-brick-display/site/downloads/parts/BR-05x04-H096.stl

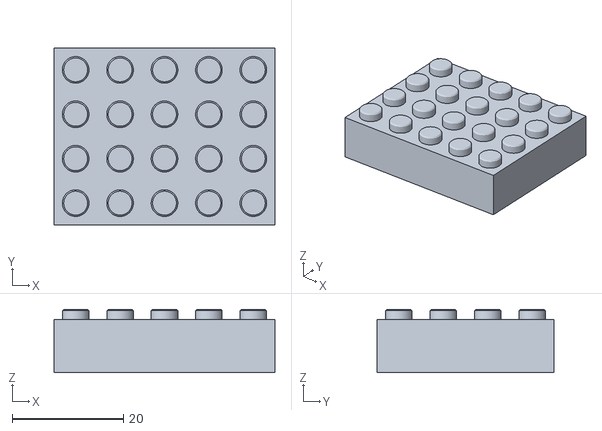
[picture p114: CAD file, 2026-09-19]
site/downloads/parts/BR-05x04-H096.stl
39.8 x 31.8 x 11.4
