ktanino10/copilot-brick-display/site/downloads/parts/BR-02x06-H064.stl

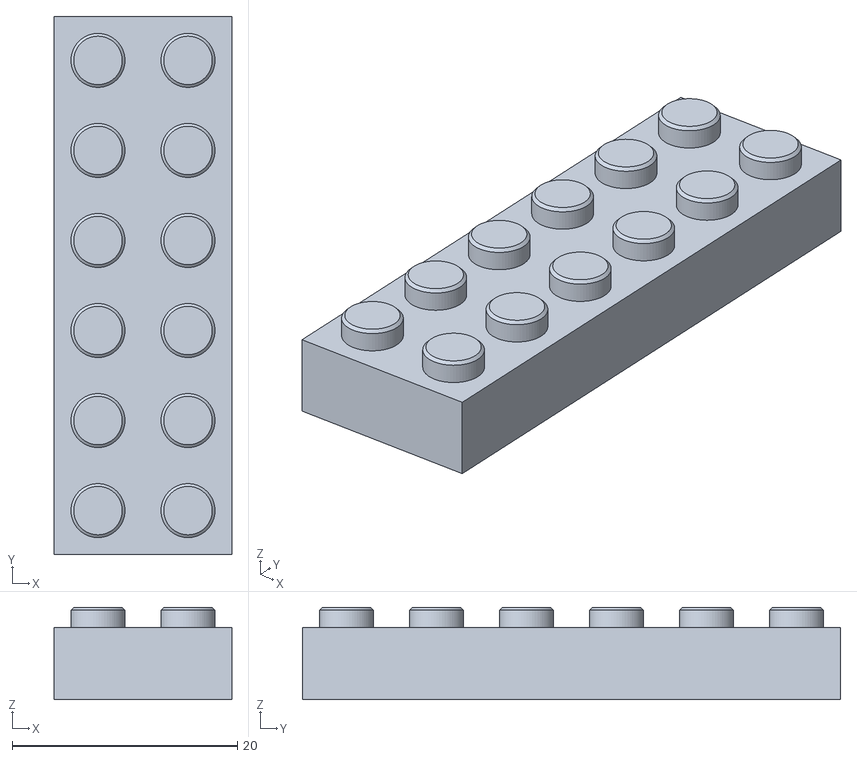
[picture p116: CAD file, 2026-09-19]
site/downloads/parts/BR-02x06-H064.stl
15.8 x 47.8 x 8.20
