ktanino10/copilot-brick-display/site/downloads/parts/FIT-F-CP12.stl

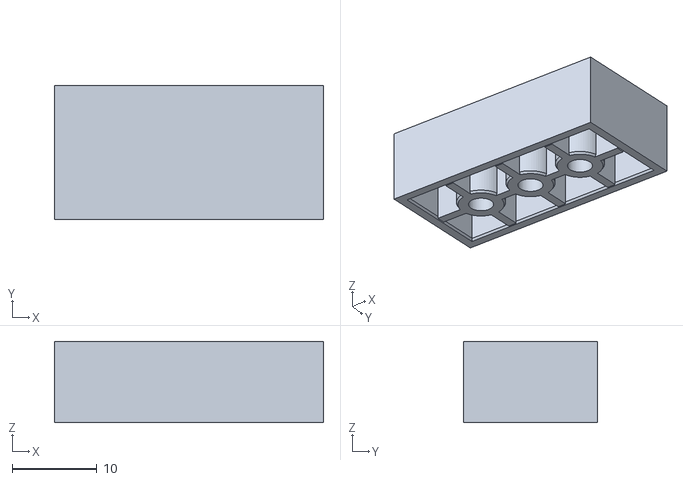
[picture p117: CAD file, 2026-09-19]
site/downloads/parts/FIT-F-CP12.stl
31.8 x 15.8 x 9.60
