ktanino10/copilot-brick-display/site/downloads/parts/BR-02x10-H096.stl

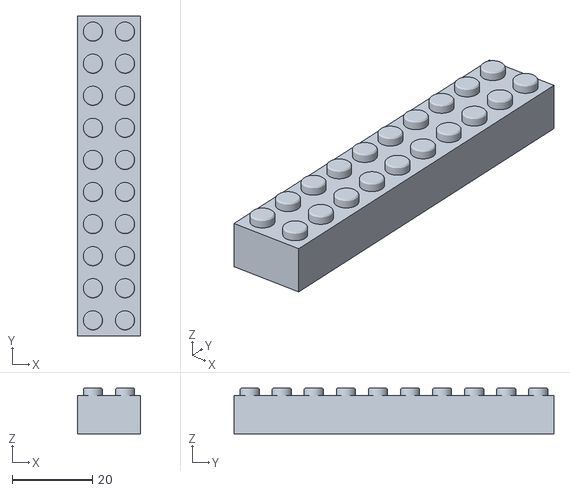
[picture p120: CAD file, 2026-09-19]
site/downloads/parts/BR-02x10-H096.stl
15.8 x 79.8 x 11.4
