ktanino10/copilot-brick-display/site/downloads/parts/BR-01x02-H096.stl

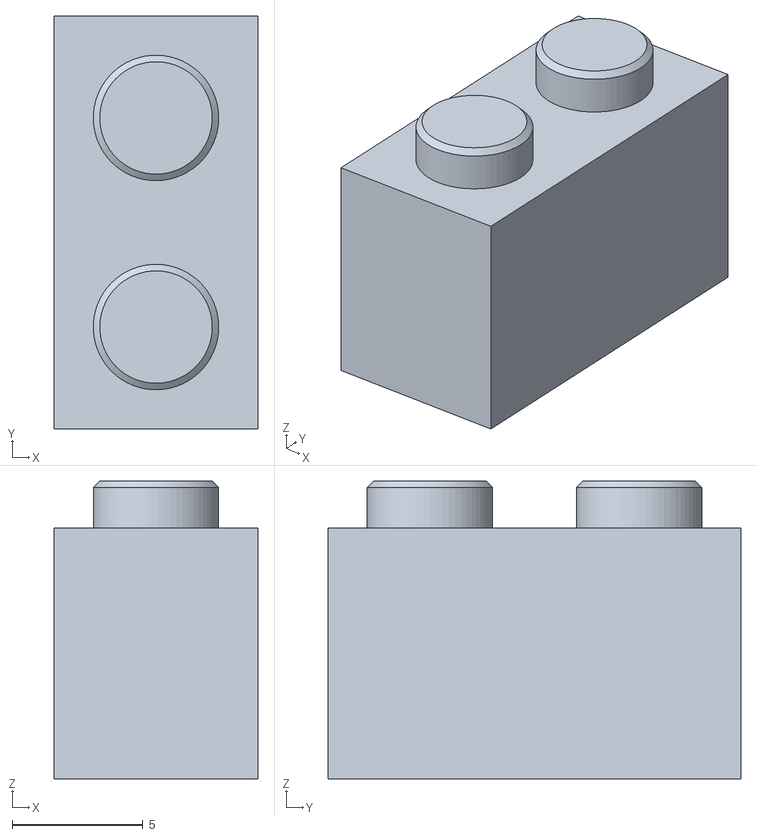
[picture p122: CAD file, 2026-09-19]
site/downloads/parts/BR-01x02-H096.stl
7.80 x 15.8 x 11.4
