ktanino10/copilot-brick-display/site/downloads/parts/BR-04x04-H064.stl

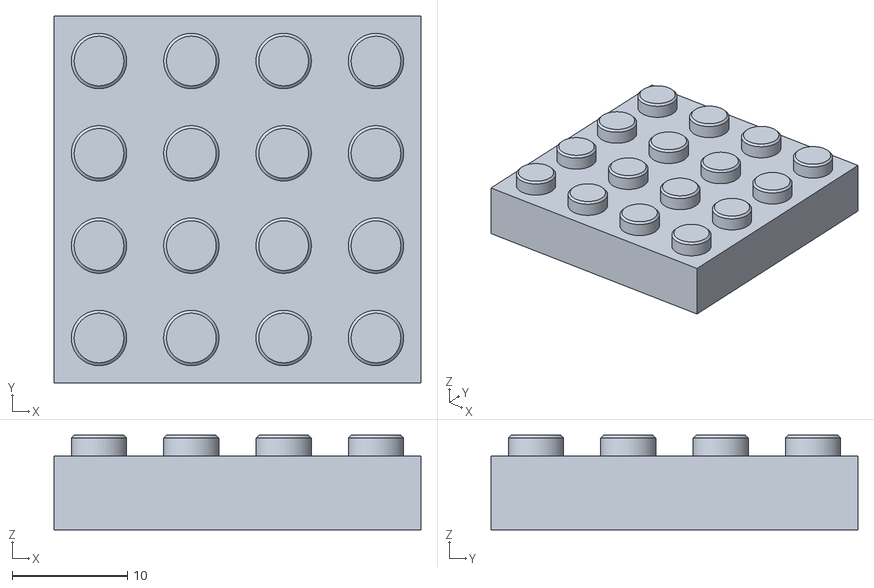
[picture p123: CAD file, 2026-09-19]
site/downloads/parts/BR-04x04-H064.stl
31.8 x 31.8 x 8.20
