ktanino10/copilot-brick-display/site/downloads/parts/BR-04x07-H096.stl

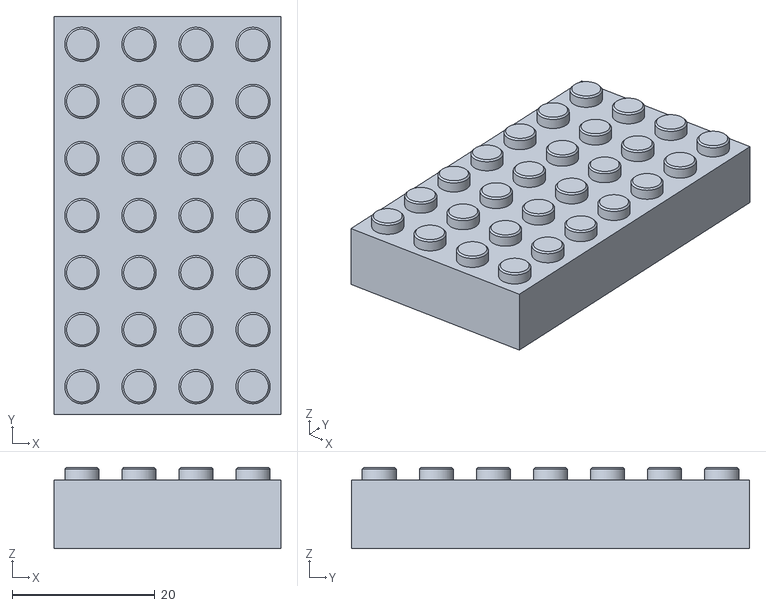
[picture p124: CAD file, 2026-09-19]
site/downloads/parts/BR-04x07-H096.stl
31.8 x 55.8 x 11.4
