ktanino10/copilot-brick-display/site/downloads/parts/BR-03x06-H096.stl

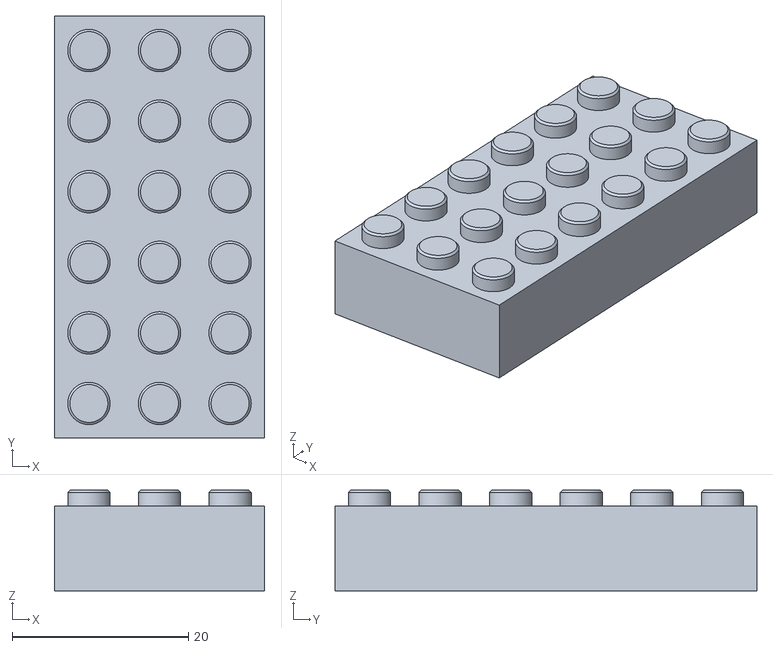
[picture p126: CAD file, 2026-09-19]
site/downloads/parts/BR-03x06-H096.stl
23.8 x 47.8 x 11.4
