ktanino10/copilot-brick-display/site/downloads/parts/FIT-M-D480.stl

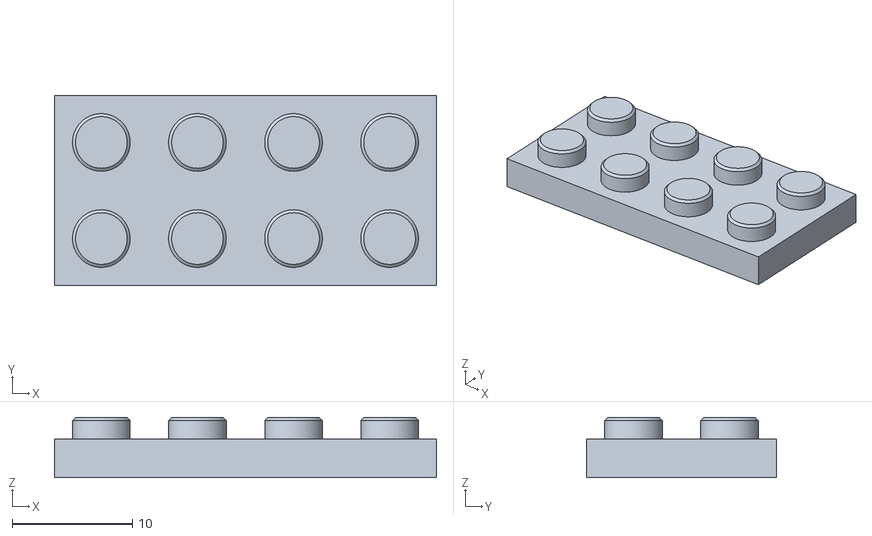
[picture p127: CAD file, 2026-09-19]
site/downloads/parts/FIT-M-D480.stl
31.8 x 15.8 x 5.00
