ktanino10/copilot-brick-display/site/downloads/parts/BR-01x06-H096.stl

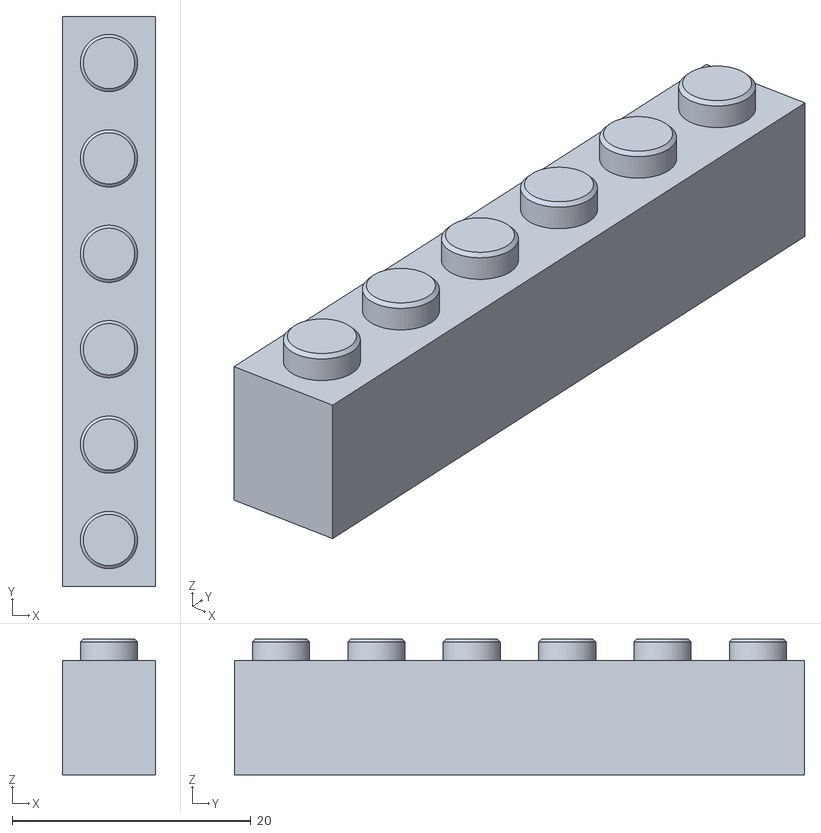
[picture p128: CAD file, 2026-09-19]
site/downloads/parts/BR-01x06-H096.stl
7.80 x 47.8 x 11.4
