ktanino10/copilot-brick-display/site/downloads/parts/BR-02x02-H096.stl

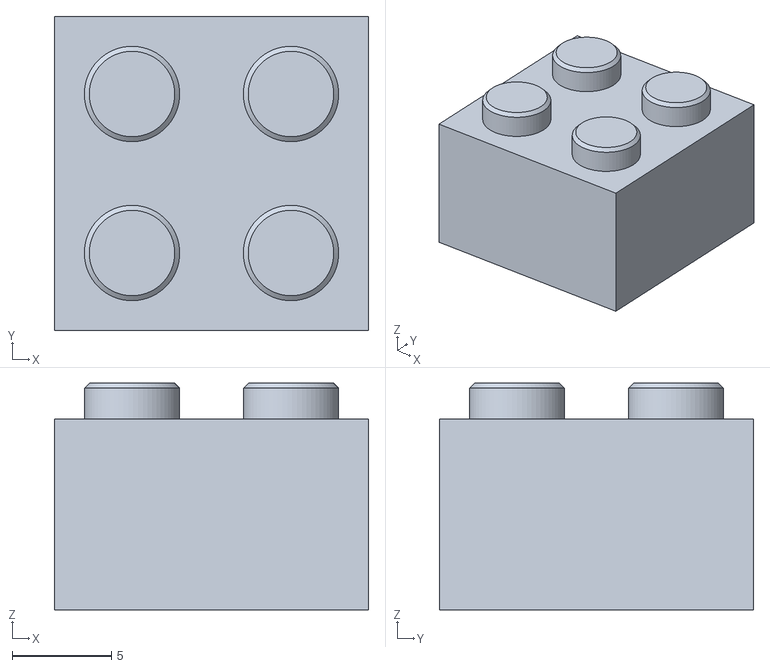
[picture p132: CAD file, 2026-09-19]
site/downloads/parts/BR-02x02-H096.stl
15.8 x 15.8 x 11.4
