ktanino10/copilot-brick-display/site/downloads/parts/BR-04x06-H096.stl

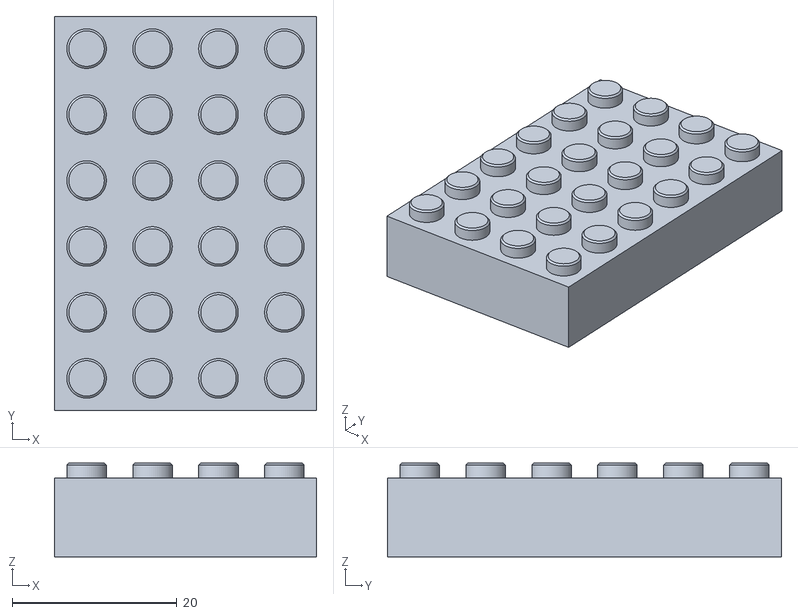
[picture p135: CAD file, 2026-09-19]
site/downloads/parts/BR-04x06-H096.stl
31.8 x 47.8 x 11.4
